JolonB/Pico-Steno/src/i2c_conf.py

USING_I2C = False
"""Whether to use the I2C expander"""

# Custom I2C key functions
# Feel free to import any functions or key types to add to this file
I2C_KEY0 = None
I2C_KEY1 = None
I2C_KEY2 = None
I2C_KEY3 = None
I2C_KEY4 = None
I2C_KEY5 = None
I2C_KEY6 = None
